cycfi/nexus/cad_drawings/cv_switch.pdf

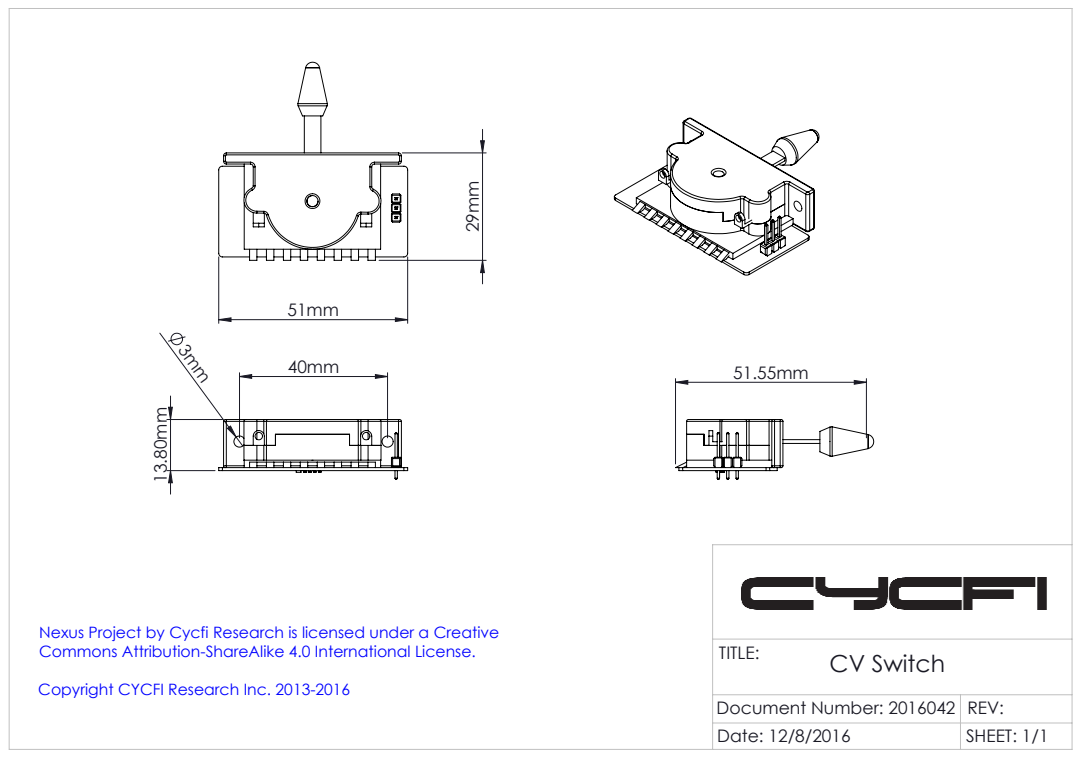
[picture p9: page 1]

Nexus Project by Cycfi Research is licensed under a Creative
Commons Attribution-ShareAlike 4.0 International License.
Copyright CYCFI Research Inc. 2013-2016 (http://creativecommons.org/licenses/by-sa/4.0/)

CV Switch TITLE:

Document Number: 2016042 | REV:
Date: 12/8/2016 | SHEET: 1/1
