cycfi/nexus/cad_drawings/19p_connector.pdf

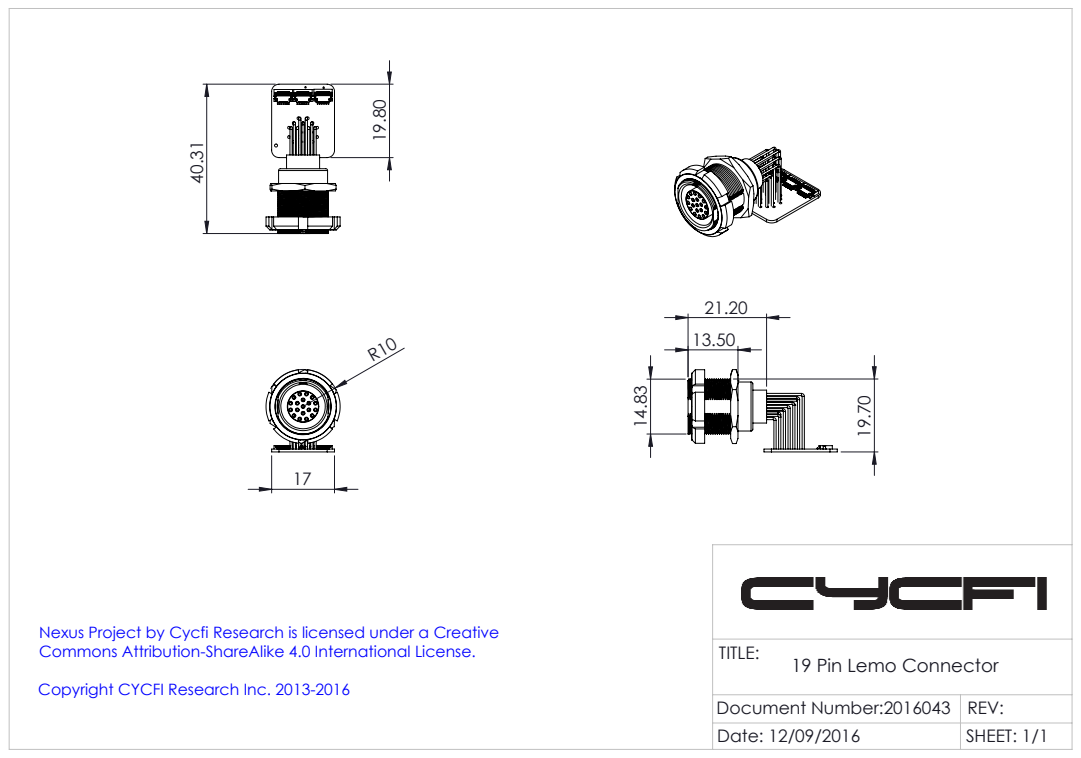
[picture p10: page 1]
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

19 Pin Lemo Connector TITLE:

Document Number:2016043 | REV:
Date: 12/09/2016 | SHEET: 1/1
