cycfi/nexus/breakout_box/main_board/main_board.pdf

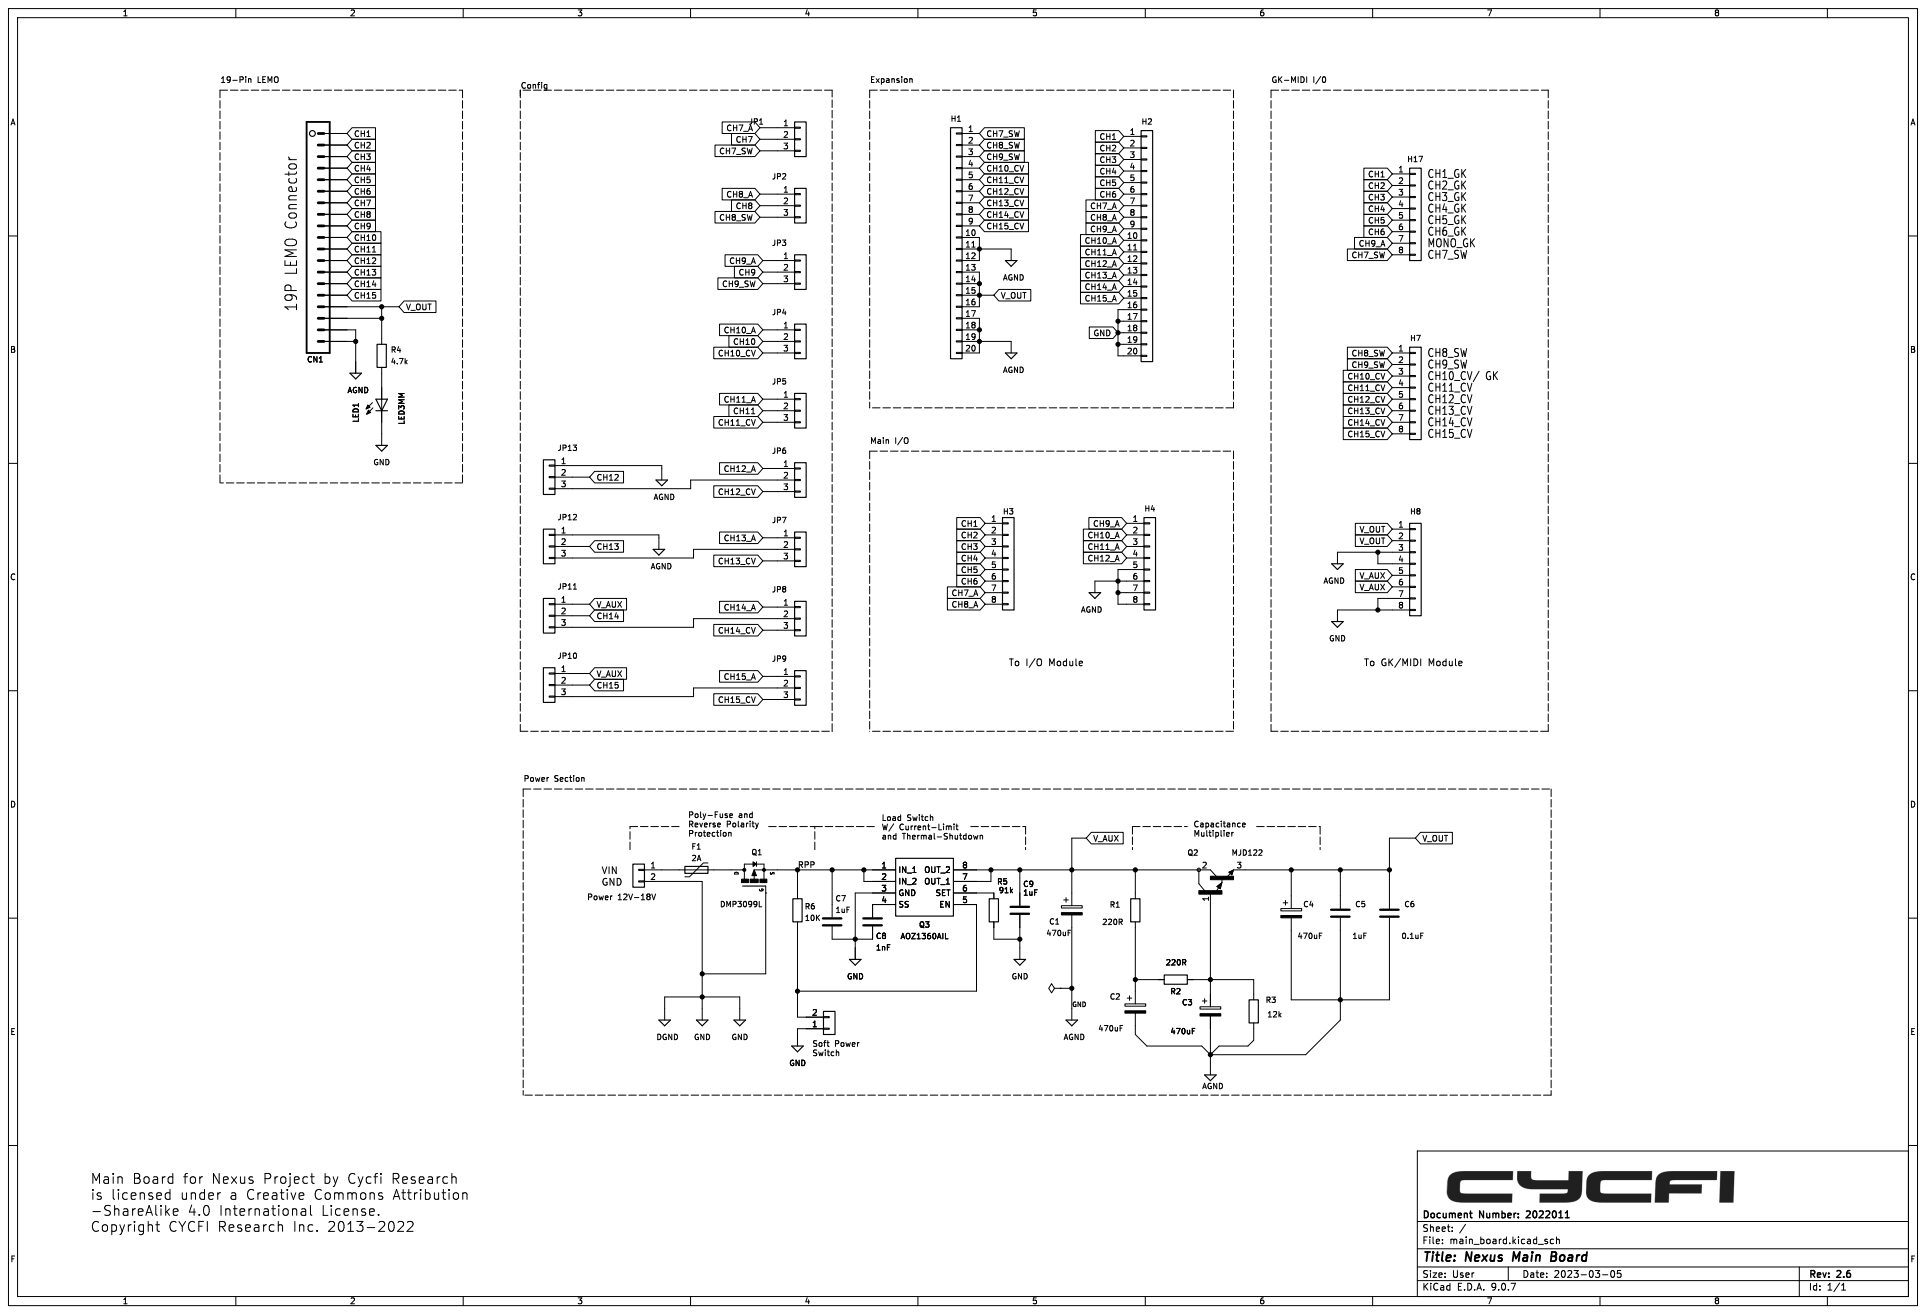
[picture p11: page 1]

Main Board for Nexus Project by Cycfi Research
is licensed under a Creative Commons Attribution
Copyright CYCFI Research Inc. 2013-2022
