cycfi/nexus/Guitar_Electronics/CV_Switch/CV_Switch_Schematics.pdf

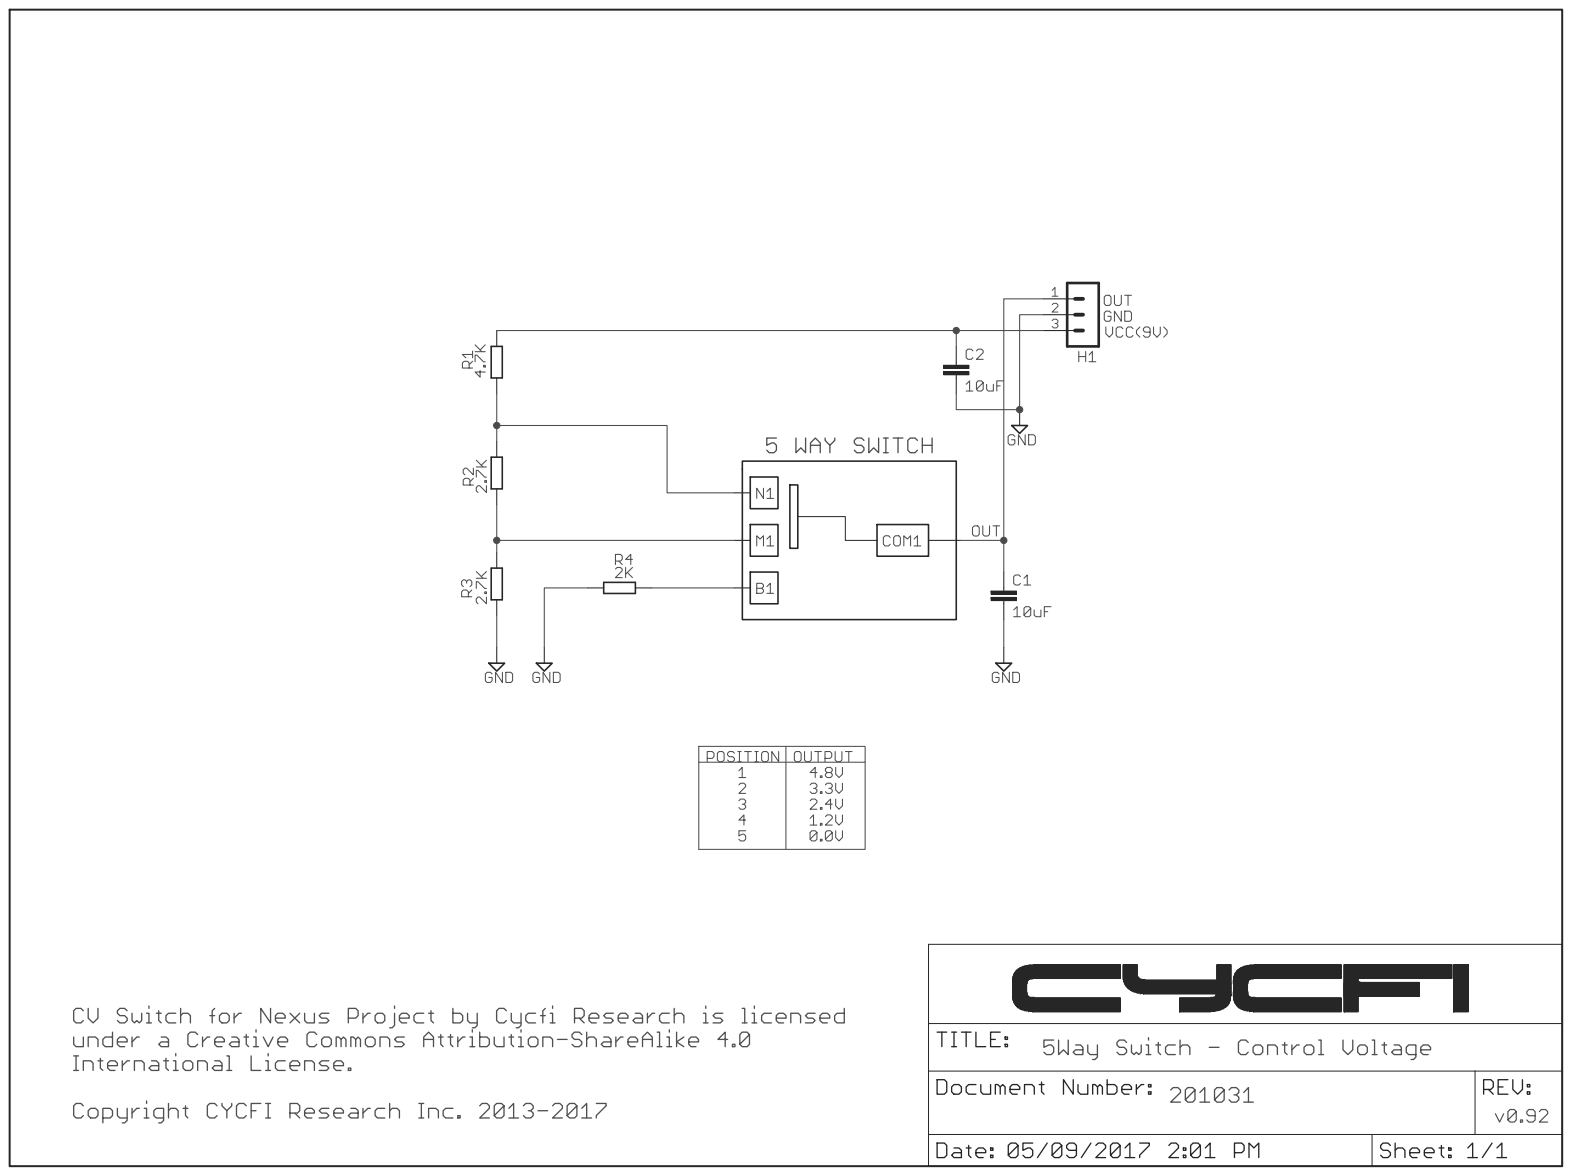
[picture p27: page 1]
