cycfi/nexus/cad_drawings/nexus.pdf

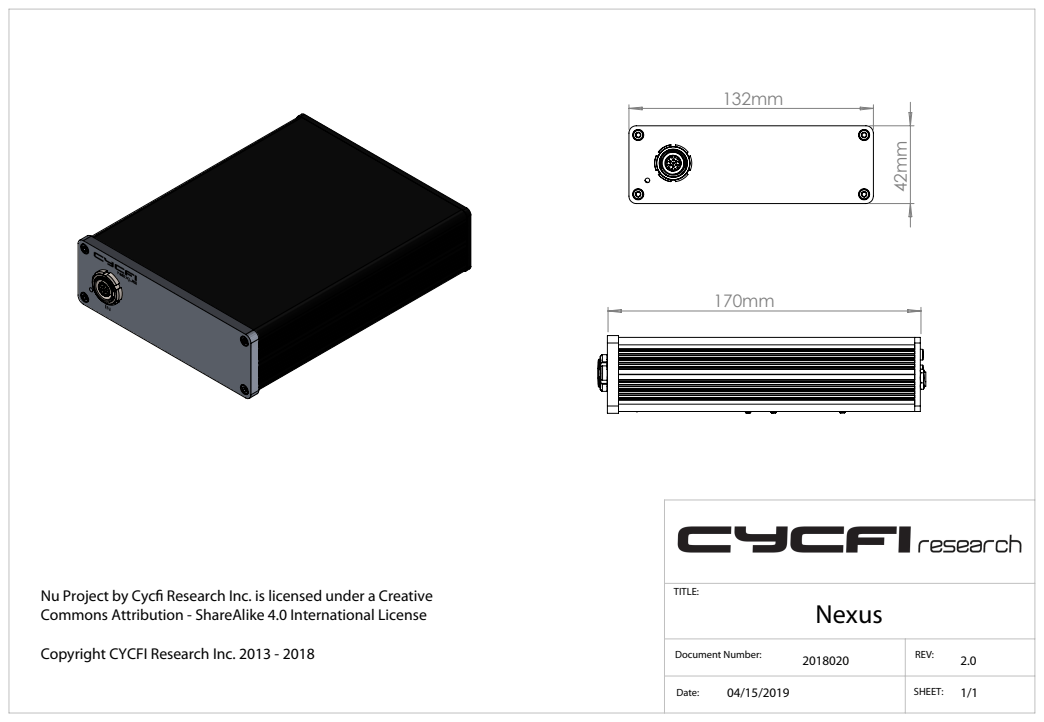
[picture p28: page 1]
Nexus; TITLE:

Nu Project by Cyc Research Inc. is licensed under a Creative
Commons Attribution - ShareAlike 4.0 International License

Copyright CYCFI Research Inc. 2013 - 2018

Document Number: 2018020 | REV: 2.0

Date: 04/15/2019 | SHEET: 1/1
