cycfi/nexus/cad_drawings/nexus_back_panel.pdf

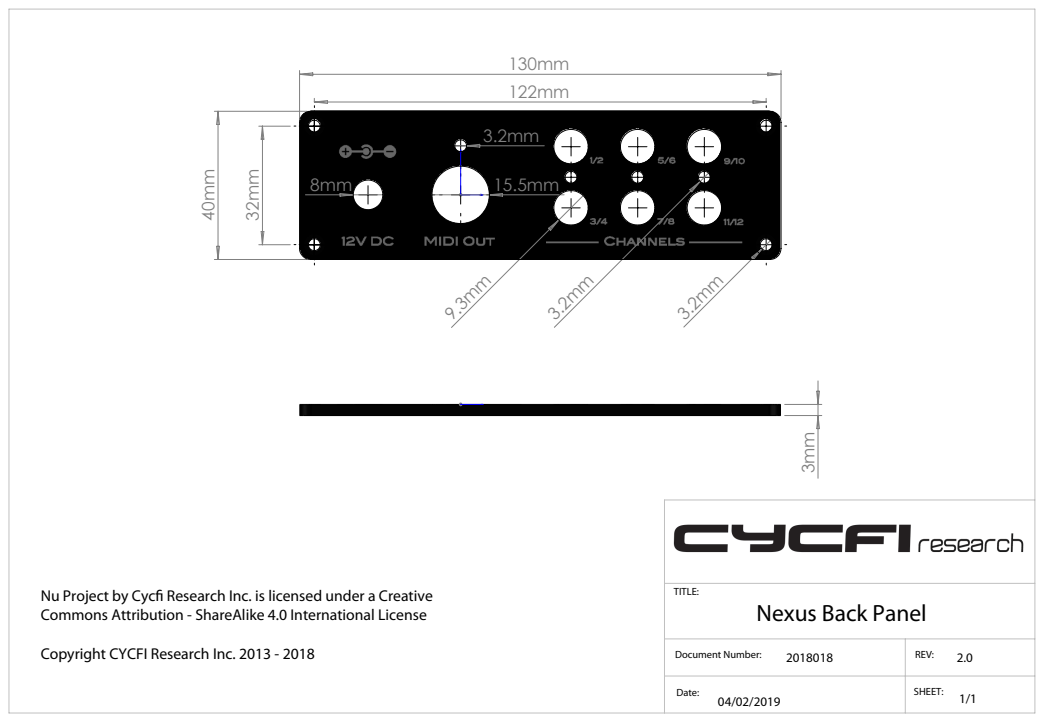
[picture p29: page 1]
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

TITLE:
Nexus Back Panel

Copyright CYCFI Research Inc. 2013 - 2018

Document Number: 2018018 | REV: 2.0

Date: 04/02/2019 | SHEET: 1/1
