cycfi/nexus/cad_drawings/nexus_front_panel.pdf

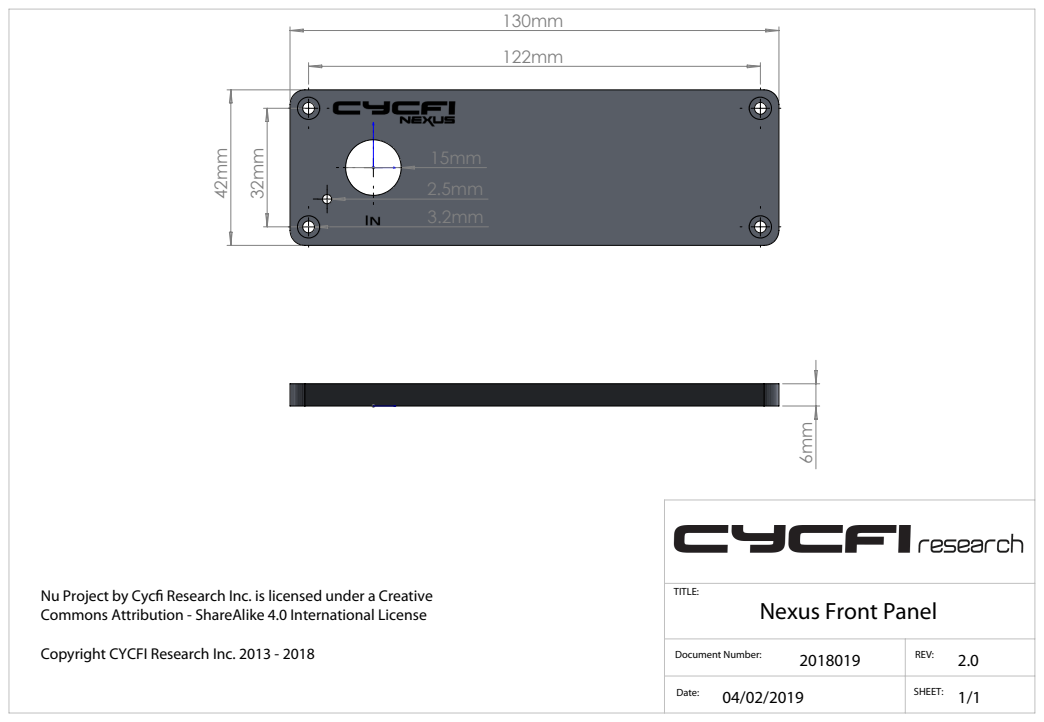
[picture p30: page 1]
TITLE:

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

Nexus Front Panel

Copyright CYCFI Research Inc. 2013 - 2018

Document Number: 2018019 | REV: 2.0
Date: 04/02/2019 | SHEET: 1/1
