cycfi/nexus/cad_drawings/cv_pot.pdf

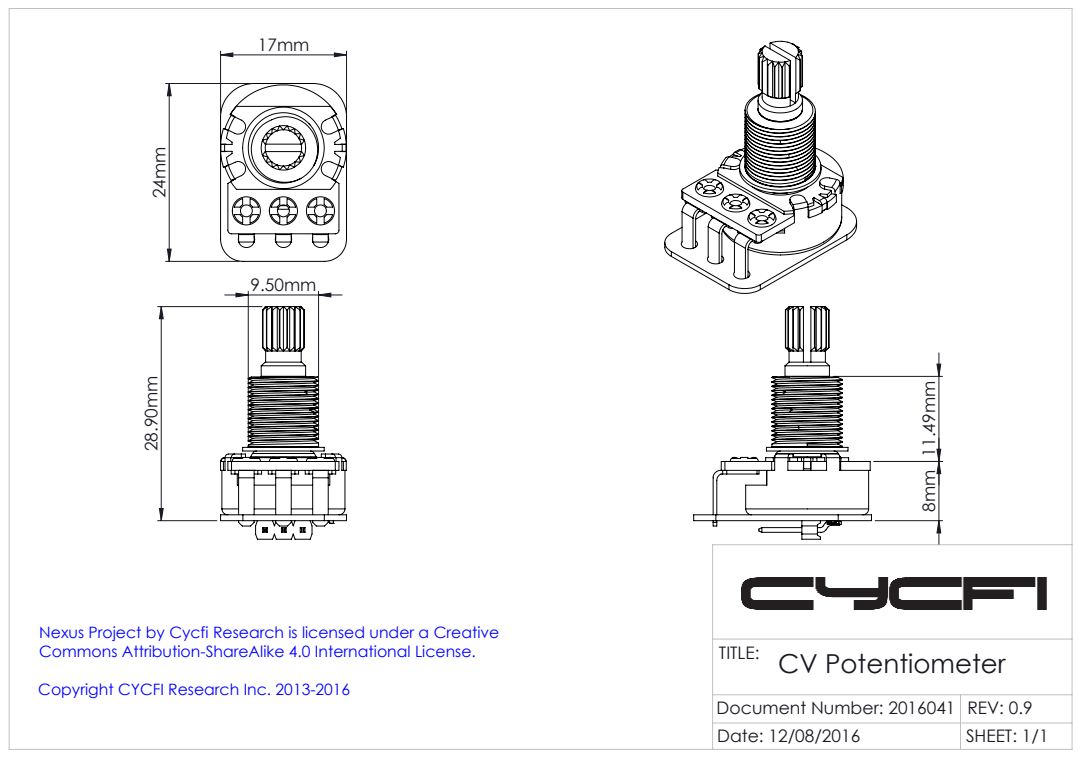
[picture p31: page 1]
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

CV Potentiometer TITLE:

Document Number: 2016041 | REV: 0.9
Date: 12/08/2016 | SHEET: 1/1
