cycfi/nexus/source/nexus_midi/util.hpp

/*==============================================================================
   Copyright (c) 2016 Cycfi Research

   Distributed under the MIT License [ https://opensource.org/licenses/MIT ]
==============================================================================*/
#if !defined(CYCFI_UTIL_HPP_NOVEMBER_11_2016)
#define CYCFI_UTIL_HPP_NOVEMBER_11_2016
//
#include <stdint.h>
#include <energia.h>

namespace cycfi
{
   ////////////////////////////////////////////////////////////////////////////
   // Small signed-integer helpers (constexpr implies inline).
   ////////////////////////////////////////////////////////////////////////////
   constexpr int32_t iabs(int32_t x)
   {
      return x < 0 ? -x : x;
   }

   // Branch-free clamp. Assumes lo <= hi with small operands (no
   // subtraction overflow), which holds at every call site. Adds the low
   // correction when x < lo, the high one when x > hi.
   constexpr int32_t clamp(int32_t x, int32_t lo, int32_t hi)
   {
      return x + ((lo - x) & -int32_t(x < lo))
               + ((hi - x) & -int32_t(x > hi));
   }

   ////////////////////////////////////////////////////////////////////////////
   // debouncer: A switch debouncer
   ////////////////////////////////////////////////////////////////////////////
   template <int samples = 10>
   struct debouncer
   {
      debouncer()
       : counter(0)
       , result(false)
      {}

      bool operator()(bool sw)
      {
         if (sw)
         {
            if (counter == samples)
               result = true;
            else
               ++counter;
         }
         else
         {
            if (counter == 0)
               result = false;
            else
               --counter;
         }
         return result;
      }

      void init(bool sw)
      {
         counter = sw ? samples : 0;
         result = sw;
      }

   private:

      int counter;
      bool result;
   };

   ////////////////////////////////////////////////////////////////////////////
   // edge_detector: A switch edge detector
   ////////////////////////////////////////////////////////////////////////////
   template <int samples = 10>
   struct edge_detector : debouncer<samples>
   {
      typedef debouncer<samples> base_type;

      edge_detector()
       : prev(false)
      {}

      int operator()(bool sw)
      {
         bool curr = base_type::operator()(sw);
         if (prev != curr)
         {
            prev = curr;
            return curr ? 1 : -1;
         }
         return 0;
      }

      void init(bool sw)
      {
         base_type::init(sw);
         prev = sw;
      }

   private:

      bool prev;
   };

   ////////////////////////////////////////////////////////////////////////////
   // repeat_button: A key detector with delay and repeat rate
   ////////////////////////////////////////////////////////////////////////////
   template <int delay_ = 1000, int rate = 100, int samples = 10>
   struct repeat_button : edge_detector<samples>
   {
      typedef edge_detector<samples> base_type;

      repeat_button()
       : start_time(-1)
      {}

      bool operator()(bool sw)
      {
         int state = base_type::operator()(sw);

         // rising edge
         if (state == 1)
         {
            start_time = millis();
            delay = delay_; // initial delay
            return true;
         }

         // falling edge
         else if (state == -1)
         {
            // reset
            start_time = -1;
            return false;
         }

         if (start_time == -1)
            return 0;

         // repeat button handling
         int now = millis();
         if (now > (start_time + delay))
         {
            start_time = now;
            delay = rate; // repeat delay
            return true;
         }
         return 0;
      }
      int start_time;
      int delay;
   };

   ////////////////////////////////////////////////////////////////////////////
   // Basic leaky-integrator filter. k will determine the effect of the
   // filter. Choose k to be a power of 2 for efficiency (the compiler
   // will optimize the computation using shifts). k = 16 is a good starting
   // point.
   //
   // This simulates the RC filter in digital form. The equation is:
   //
   //    y[i] = rho * y[i-1] + s
   //
   // where rho < 1. To avoid floating point, we use k instead which
   // allows for integer operations. In terms of k, rho = 1 - (1 / k).
   // So the actual formula is:
   //
   //    y[i] += s - (y[i-1] / k);
   //
   // k will also be the filter gain, so the final result should be
   // divided by k.
   //
   ////////////////////////////////////////////////////////////////////////////
   template <int k, typename T = int>
   struct lowpass
   {
      lowpass()
       : y(0)
      {}

      T operator()(T s)
      {
         y += s - (y / k);
         return y / k;
      }

      T y;
   };

   //////////////////////////////////////////////////////////////////////////////
   // dynamic_smoother: an adaptive lowpass. Fixed-point (Q8) integer port
   // of the Q DSP dynamic_smoother (Andrew Simper, "Dynamic Smoothing Using
   // Self Modulating Filter", Cytomic, 2016). Two one-pole integrators
   // (low1, low2) whose shared cutoff g is opened by the bandpass magnitude
   // |low1 - low2|, so it tracks fast transients with little lag but smooths
   // hard when stable. State is kept in Q8 (x256) for sub-LSB precision.
   //
   //    G0:    base cutoff in Q8 [0..256] (g = G0/256 at rest). Lower = more
   //           smoothing / more lag at rest.
   //    Sense: how strongly the bandpass opens the cutoff on a move; 0 = a
   //           plain fixed two-pole lowpass at cutoff G0. A power of two
   //           compiles the sense term to a shift.
   //////////////////////////////////////////////////////////////////////////////
   template <int G0, int Sense, typename T = int32_t>
   struct dynamic_smoother
   {
      dynamic_smoother()
       : low1(0), low2(0)
      {}

      // Seed both integrators to a known 10-bit value (e.g. at startup).
      dynamic_smoother& operator=(T s)
      {
         low1 = low2 = s << 8;
         return *this;
      }

      T operator()(T s)
      {
         T band = low1 - low2;
         if (band < 0)
            band = -band;
         int32_t g = G0 + ((int32_t(Sense) * (band >> 8)) >> 8);
         if (g > 256)
            g = 256;
         low1 += int32_t(g) * ((s << 8) - low1) >> 8;
         low2 += int32_t(g) * (low1 - low2) >> 8;
         return low2 >> 8;
      }

      // |low1 - low2| (Q8): the bandpass magnitude -- ~0 at rest, large on
      // a move. A ready-made velocity signal (e.g. to gate a center detent
      // off during vibrato).
      T band() const
      {
         T b = low1 - low2;
         return b < 0 ? -b : b;
      }

      T low1;
      T low2;
   };

   //////////////////////////////////////////////////////////////////////////////
   // dc_servo: tracks the slow DC baseline of a signal, but only while the
   // input is STILL (caller-supplied) and near the current estimate
   // (|x - c| <= Gate), and hard-clamped to +/-Clip of a fixed seed. Very
   // slow (tau = 2^Shift ms), so it follows only drift/bias, never a real
   // excursion -- and the clamp means even a momentary mis-gate can't let
   // the estimate walk onto one. operator() advances the estimate by the
   // elapsed dt and returns it; seed_value() is the fixed reference the
   // clamp is centred on.
   //////////////////////////////////////////////////////////////////////////////
   template <int Shift, int Gate, int Clip>
   struct dc_servo
   {
      // int32_t(1): a bare 1<<Shift overflows the device's 16-bit int once
      // Shift >= 16.
      static_assert(((int32_t(1) << Shift) >> Shift) == 1,
                    "dc_servo scale overflows int32_t");

      dc_servo() : acc(0), seed(0) {}

      void init(int32_t s)                   // seed the estimate := s
      {
         seed = s;
         acc  = s * (int32_t(1) << Shift);
      }

      int32_t operator()(int32_t x, bool still, int32_t dt)
      {
         int32_t one = int32_t(1) << Shift;
         int32_t c   = acc >> Shift;
         if (still && iabs(x - c) <= Gate)
            acc += (x - c) * dt;          // slow leak toward baseline
         acc = clamp(acc, (seed - Clip) * one, (seed + Clip) * one);
         return acc >> Shift;
      }

      int32_t value() const { return acc >> Shift; }   // current estimate
      int32_t seed_value() const { return seed; }   // clamp's fixed centre

      int32_t acc;
      int32_t seed;
   };

   ////////////////////////////////////////////////////////////////////////////
   // moving_average: Simple boxcar FIR filter. Optimal for reducing white
   // (broadband) noise. N = 2^Shift samples. Noise is reduced by sqrt(N)
   // and latency is N/2 samples. Use a small T (e.g. int16_t) to save RAM
   // when the signal range fits -- 10-bit ADC (0-1023) fits in int16_t and
   // the sum of up to 32 samples (32x1023=32736) also fits in int16_t.
   ////////////////////////////////////////////////////////////////////////////
   template <int Shift, typename T = int32_t>
   struct moving_average
   {
      static int constexpr size = 1 << Shift;

      moving_average() : _sum(0), _index(0)
      {
         for (int i = 0; i < size; ++i)
            _buf[i] = 0;
      }

      void init(T s)
      {
         for (int i = 0; i < size; ++i)
            _buf[i] = s;
         _sum = s * size;
         _index = 0;
      }

      T operator()(T s)
      {
         _sum -= _buf[_index];
         _buf[_index] = s;
         _sum += s;
         _index = (_index + 1) & (size - 1);
         return _sum >> Shift;
      }

      T   _buf[size];
      T   _sum;
      int _index;
   };

   ////////////////////////////////////////////////////////////////////////////
   // moving_average_n: boxcar FIR over any N samples (not restricted to a
   // power of two). Costs a divide by N per sample, so prefer
   // moving_average<Shift> when N can be a power of two (it uses a shift).
   // Latency is (N-1)/2 samples.
   ////////////////////////////////////////////////////////////////////////////
   template <int Taps, typename T = int32_t>
   struct moving_average_n
   {
      moving_average_n() : _sum(0), _index(0)
      {
         for (int i = 0; i != Taps; ++i)
            _buf[i] = 0;
      }

      void init(T s)
      {
         for (int i = 0; i != Taps; ++i)
            _buf[i] = s;
         _sum = s * Taps;
         _index = 0;
      }

      T operator()(T s)
      {
         _sum -= _buf[_index];
         _buf[_index] = s;
         _sum += s;
         if (++_index == Taps)
            _index = 0;
         return _sum / Taps;
      }

      T   _buf[Taps];
      T   _sum;
      int _index;
   };

   ////////////////////////////////////////////////////////////////////////////
   // Delta gate. Returns true if the signal, s, is above or below the given
   // window. For example, if window is 5, the previous signal is 20 and the
   // current signal, s, is within 15 to 25, the function returns false,
   // otherwise true.
   ////////////////////////////////////////////////////////////////////////////
   template <unsigned default_window, typename T = int>
   struct delta_gate
   {
      delta_gate()
       : val(0)
       , window(default_window)
      {}

      void init(T s)
      {
         val = s;
      }

      void set_window(T window_)
      {
         window = window_;
      }

      bool operator()(T s)
      {
         T delta = s > val ? s - val : val - s;
         if (delta > window)
         {
            val = s;
            return true;
         }
         return false;
      }

      T val;
      T window;
   };

   ////////////////////////////////////////////////////////////////////////////
   // slew_gate: reject input steps faster than the source can physically
   // move (e.g. a contact glitch that shifts an ADC reference far quicker
   // than the real signal), holding the last good reading. A glitched level
   // is SUSTAINED, so every reading stays a too-fast jump from the held
   // value and is rejected for the whole event, while genuine motion
   // (<= Rate units/ms) passes through.
   ////////////////////////////////////////////////////////////////////////////
   template <int Rate, int Slack, int DtMax>
   struct slew_gate
   {
      slew_gate() : held(0), last(0) {}

      void init(int32_t x, uint32_t now) { held = x; last = now; }

      int32_t operator()(int32_t raw, uint32_t now)
      {
         int32_t dt = clamp(int32_t(now - last), 0, DtMax);
         last = now;
         if (iabs(raw - held) > Rate * dt + Slack)
            return held;                      // non-physical jump: hold
         held = raw;
         return raw;
      }

      int32_t  held;
      uint32_t last;
   };

   ////////////////////////////////////////////////////////////////////////////
   // stillness: "has the signal settled", by displacement-over-time. A
   // velocity or band measure can't see a slow ramp (near-zero velocity yet
   // very much moving), so watch instead whether the value has stayed within
   // Band for DwellMs. Returns true once it has held still that long.
   ////////////////////////////////////////////////////////////////////////////
   template <int Band, int DwellMs>
   struct stillness
   {
      stillness() : ref(0), since(0) {}

      void init(int32_t x, uint32_t now) { ref = x; since = now; }

      bool operator()(int32_t x, uint32_t now)
      {
         if (iabs(x - ref) > Band) { ref = x; since = now; } // restart dwell
         return now - since >= uint32_t(DwellMs);
      }

      int32_t  ref;
      uint32_t since;
   };
}

#endif
